LukasGossmann/StepperClock/Documentation/0K20HC30-064B-NK2.5-12.jpg

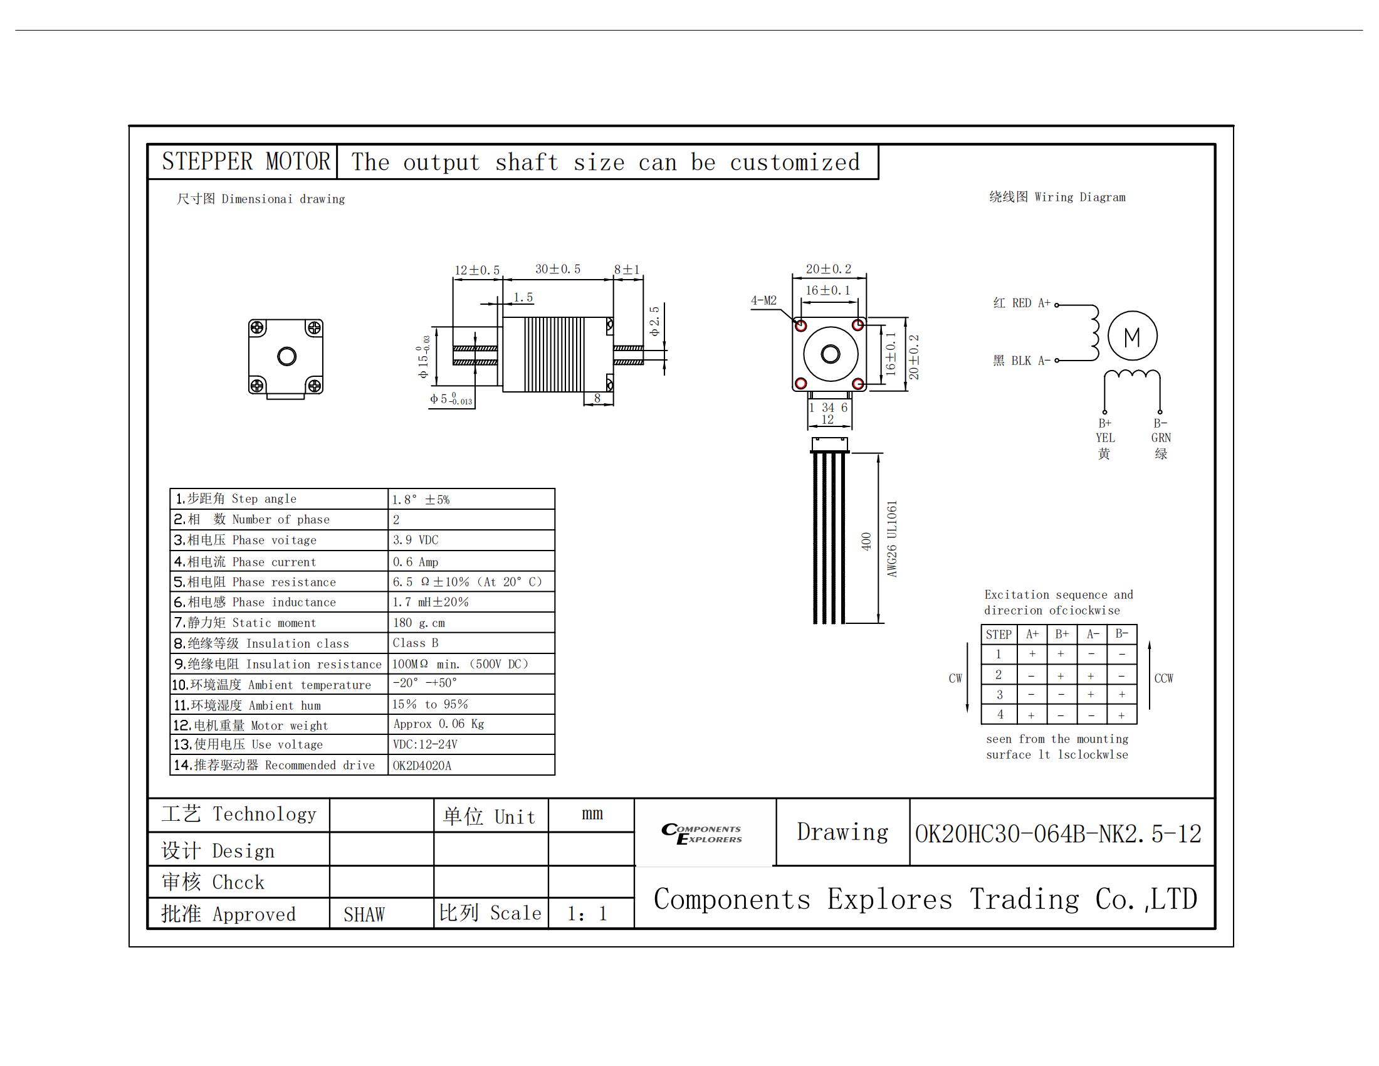
Documentation/0K20HC30-064B-NK2.5-12.jpg
