LukasGossmann/StepperClock/Documentation/0K20STH28-0604B.jpg

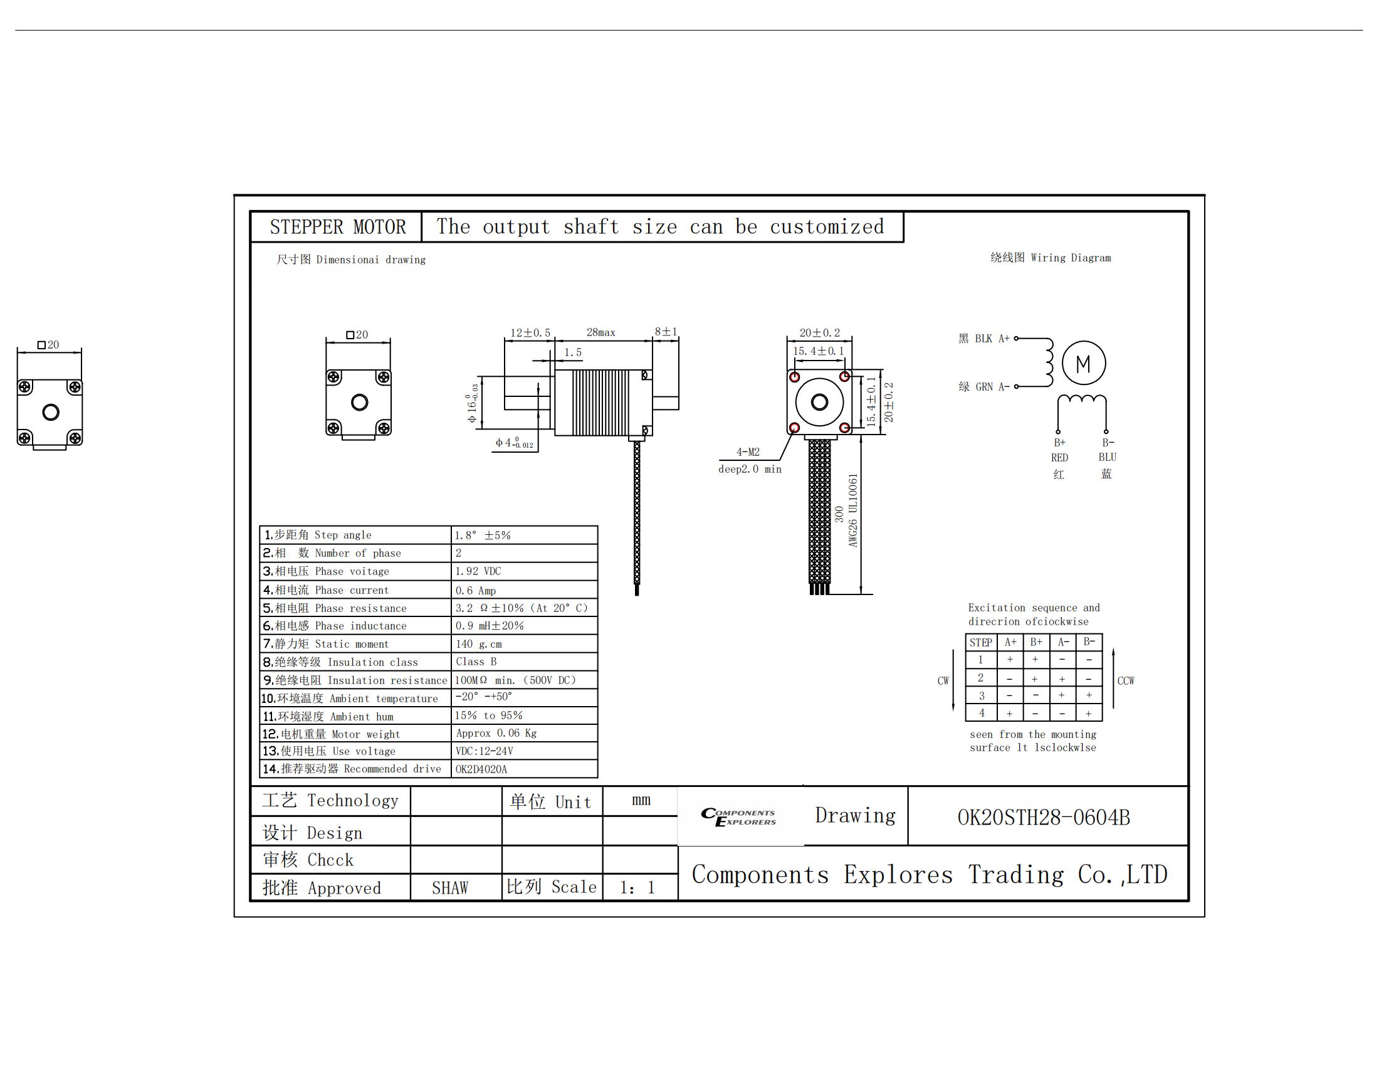
Documentation/0K20STH28-0604B.jpg
