LukasGossmann/StepperClock/Pictures/Backplate rabbet.jpg

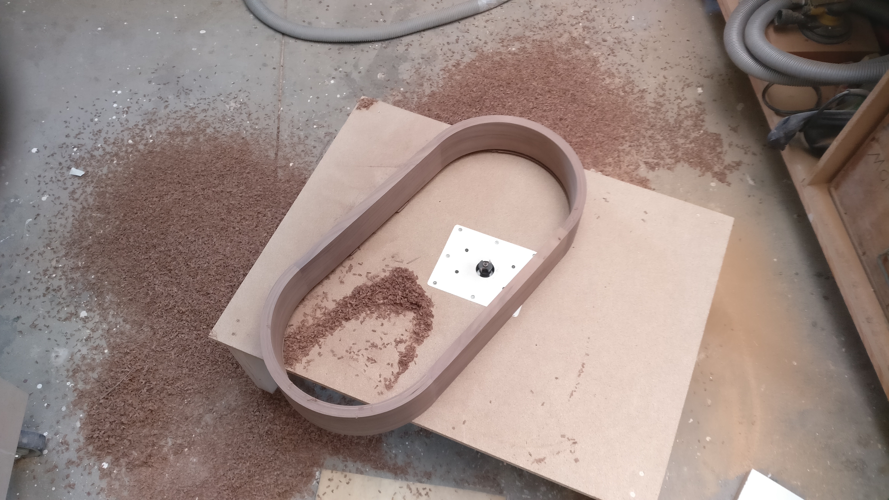
Pictures/Backplate rabbet.jpg
