LukasGossmann/StepperClock/Pictures/Backplate Veneer Back.jpg

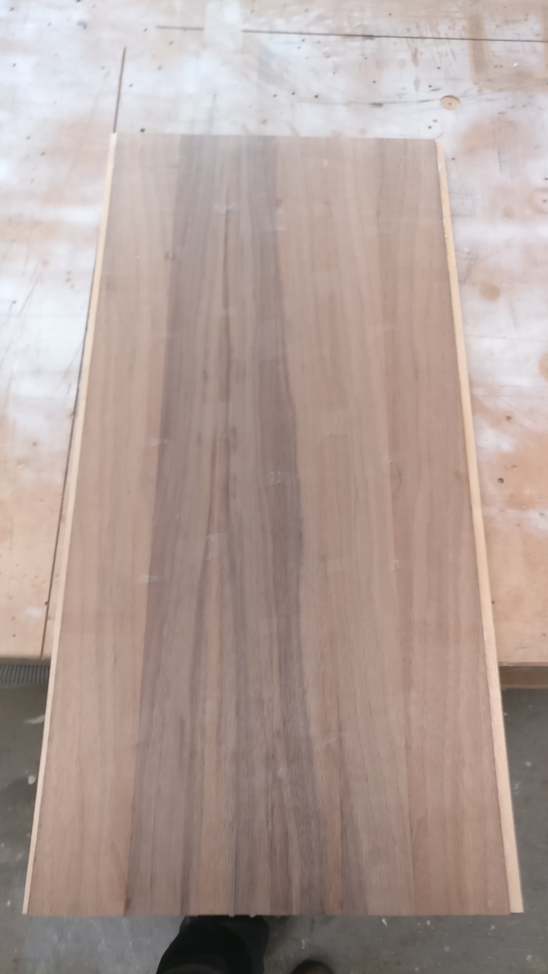
Pictures/Backplate Veneer Back.jpg
