LukasGossmann/StepperClock/Pictures/Bending Fixture 1.jpg

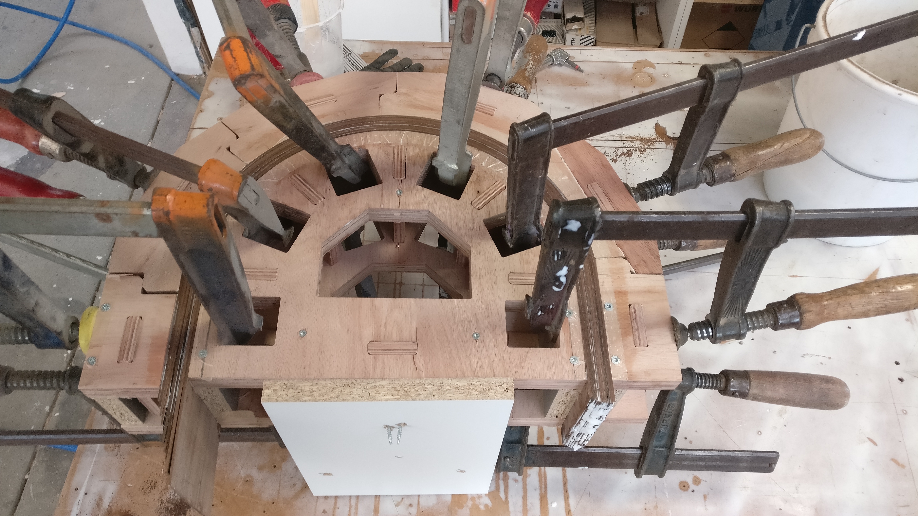
Pictures/Bending Fixture 1.jpg
