LukasGossmann/StepperClock/Pictures/Bending Fixture 2.jpg

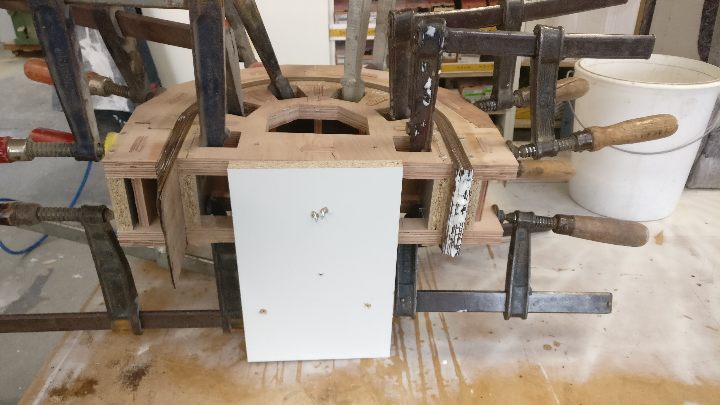
Pictures/Bending Fixture 2.jpg
