LukasGossmann/StepperClock/Pictures/Brass Rind Size.jpg

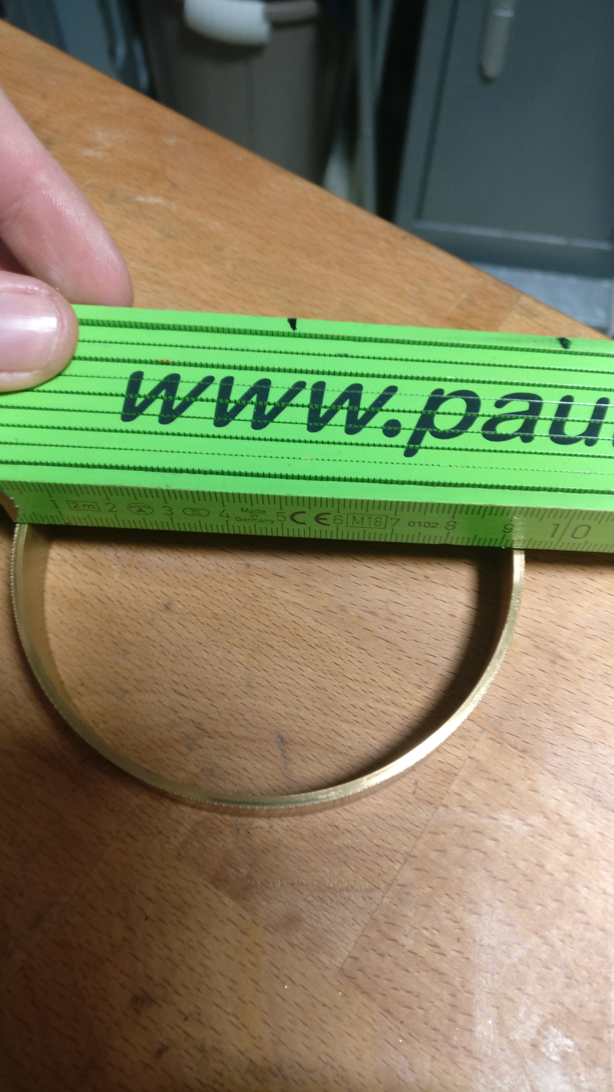
Pictures/Brass Rind Size.jpg
