LukasGossmann/StepperClock/Pictures/Brass Ring.jpg

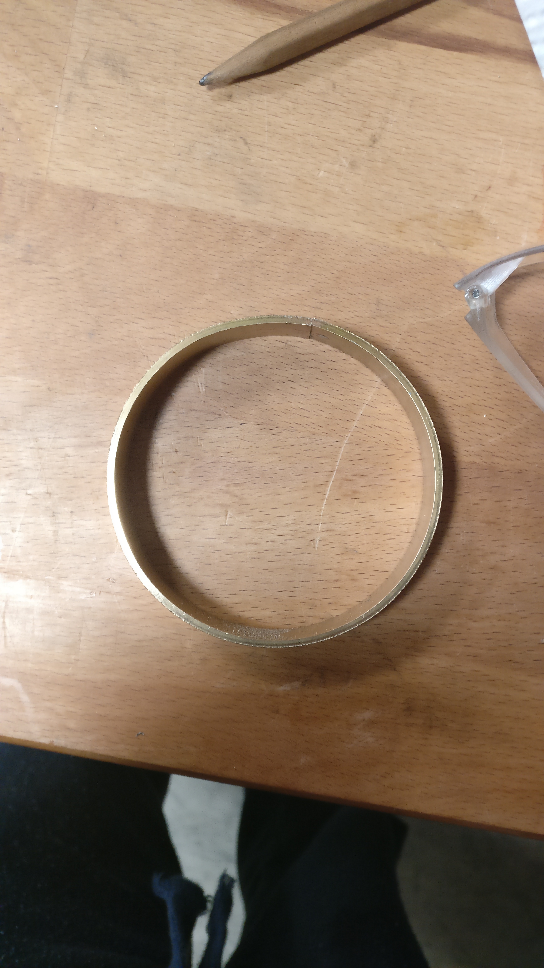
Pictures/Brass Ring.jpg
