LukasGossmann/StepperClock/Pictures/Clock Hands.jpg

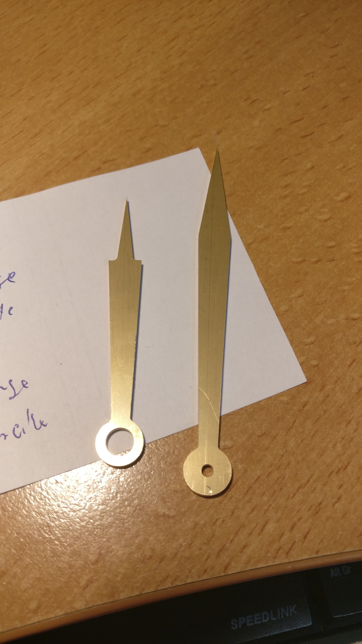
Pictures/Clock Hands.jpg
