LukasGossmann/StepperClock/Pictures/Clock on Wall.jpg

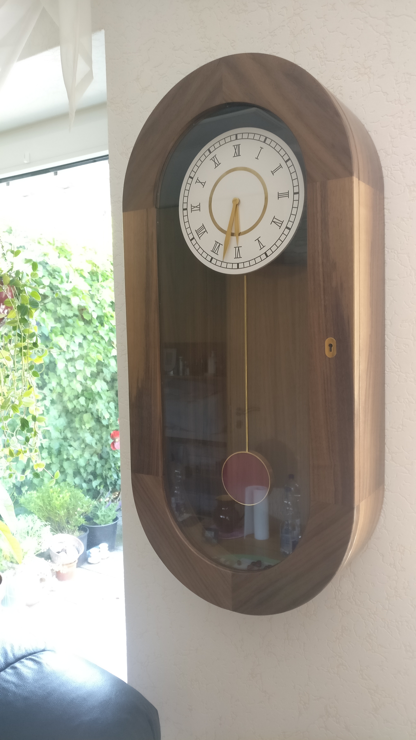
Pictures/Clock on Wall.jpg
