LukasGossmann/StepperClock/Pictures/Clock Render.png

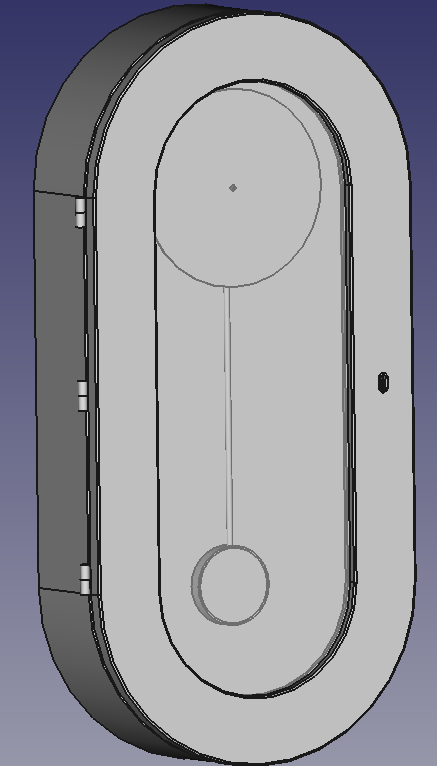
Pictures/Clock Render.png
