LukasGossmann/StepperClock/Pictures/Clockwork/BackView.png

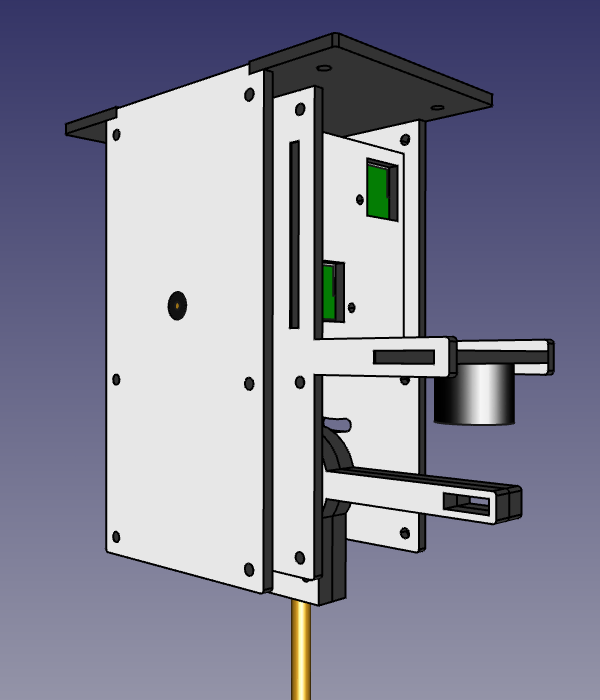
Pictures/Clockwork/BackView.png
