LukasGossmann/StepperClock/Pictures/Clockwork/FrontView.png

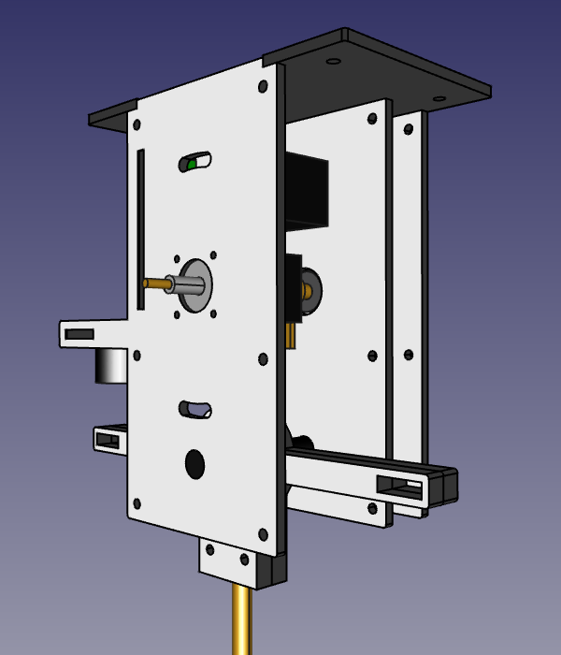
Pictures/Clockwork/FrontView.png
