LukasGossmann/StepperClock/Pictures/Domino Fixture 1.jpg

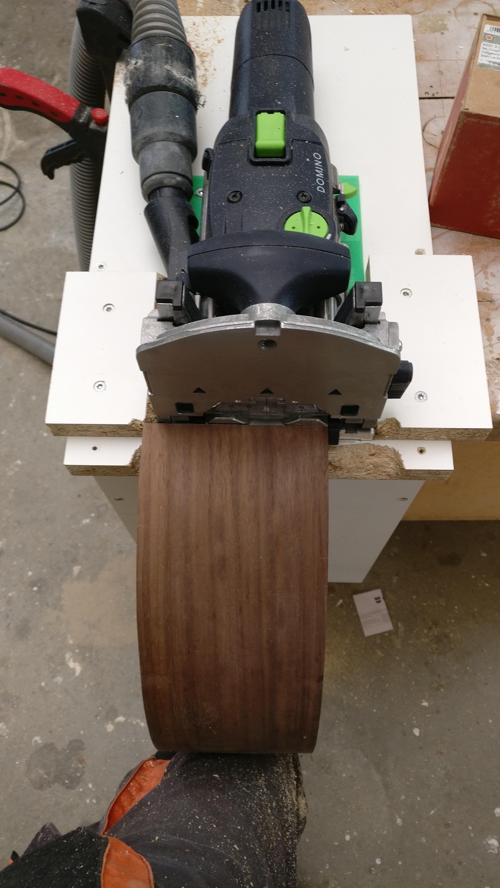
Pictures/Domino Fixture 1.jpg
