LukasGossmann/StepperClock/Pictures/Domino Fixture 2.jpg

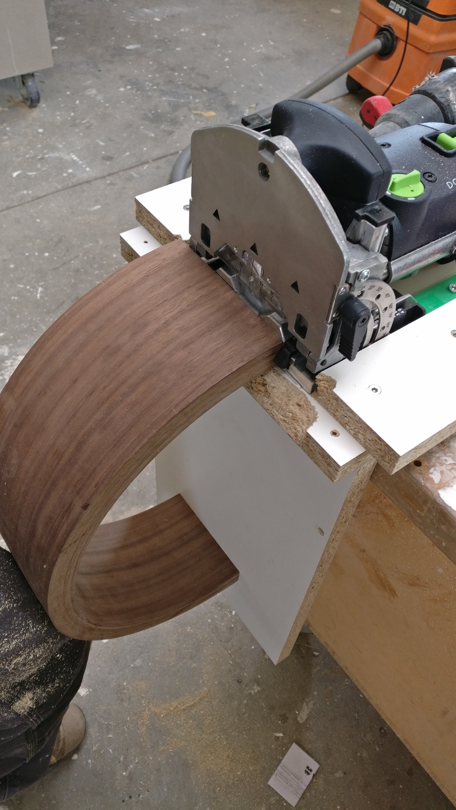
Pictures/Domino Fixture 2.jpg
