LukasGossmann/StepperClock/Pictures/Door glueup.jpg

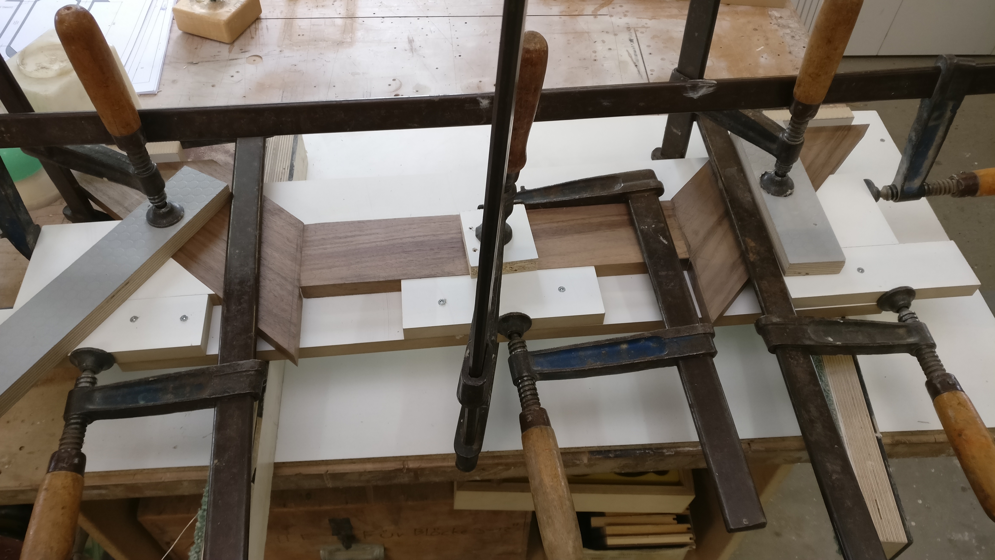
Pictures/Door glueup.jpg
