LukasGossmann/StepperClock/Pictures/Door Hindge.jpg

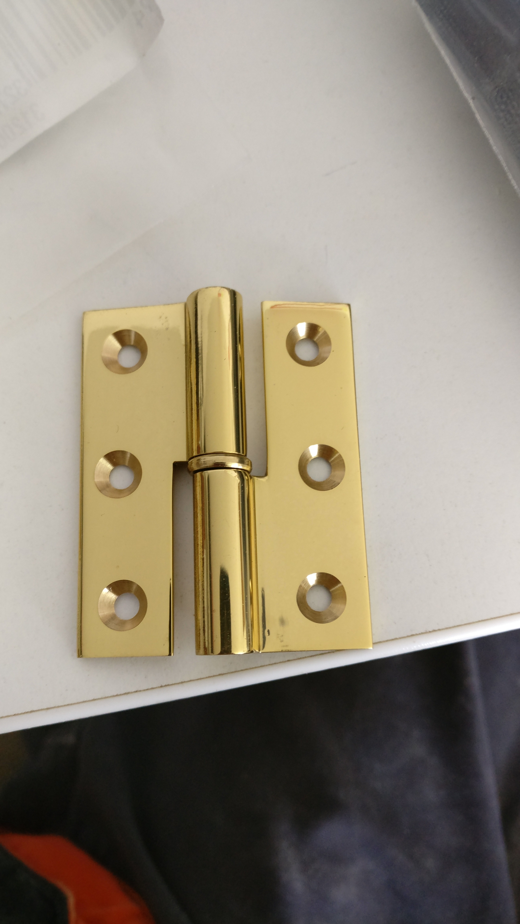
Pictures/Door Hindge.jpg
