LukasGossmann/StepperClock/Pictures/DoorLock/AngledView.png

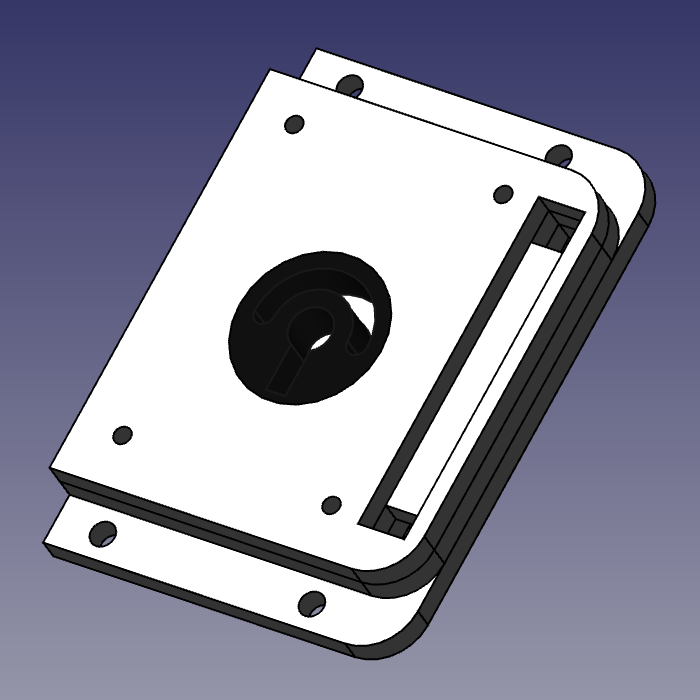
Pictures/DoorLock/AngledView.png
