LukasGossmann/StepperClock/Pictures/DoorLock/AngledView_complete.png

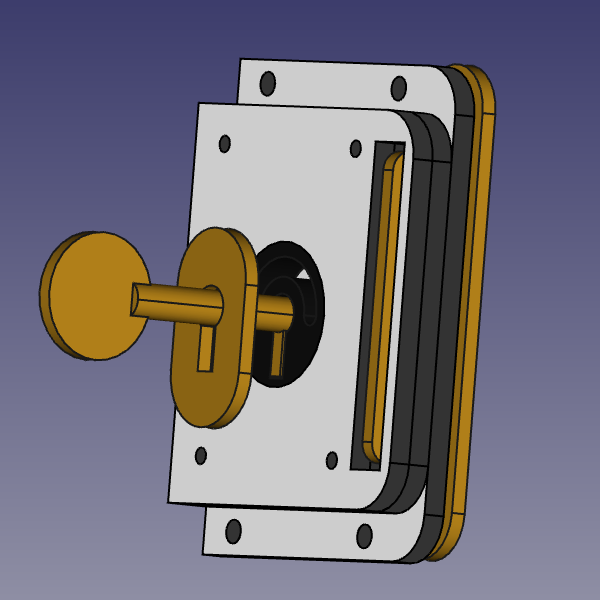
Pictures/DoorLock/AngledView_complete.png
