LukasGossmann/StepperClock/Pictures/Flush trimming bend glueup.jpg

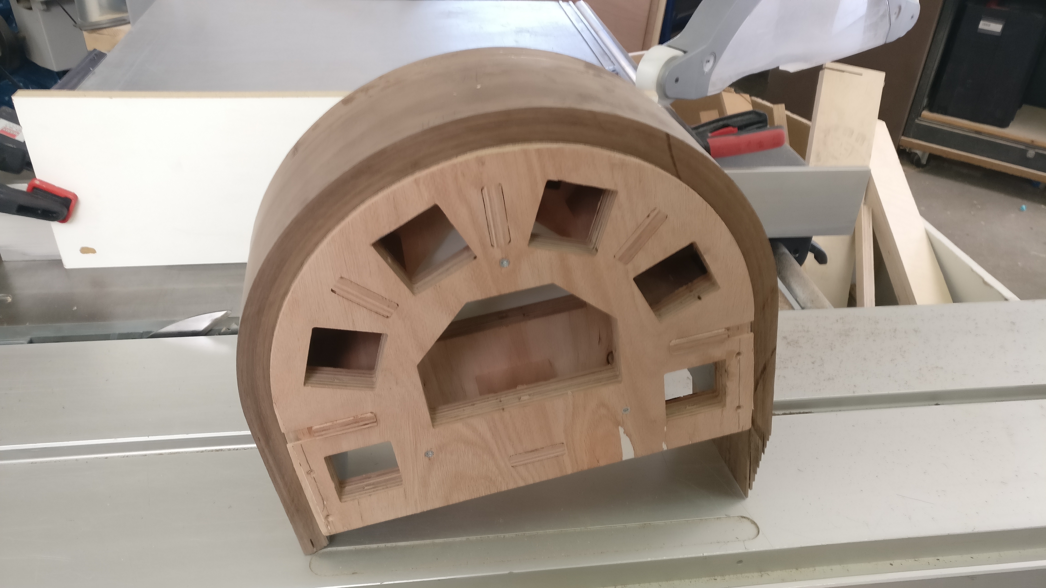
Pictures/Flush trimming bend glueup.jpg
