LukasGossmann/StepperClock/Pictures/Glass Holder Thicknessing Fixure.jpg

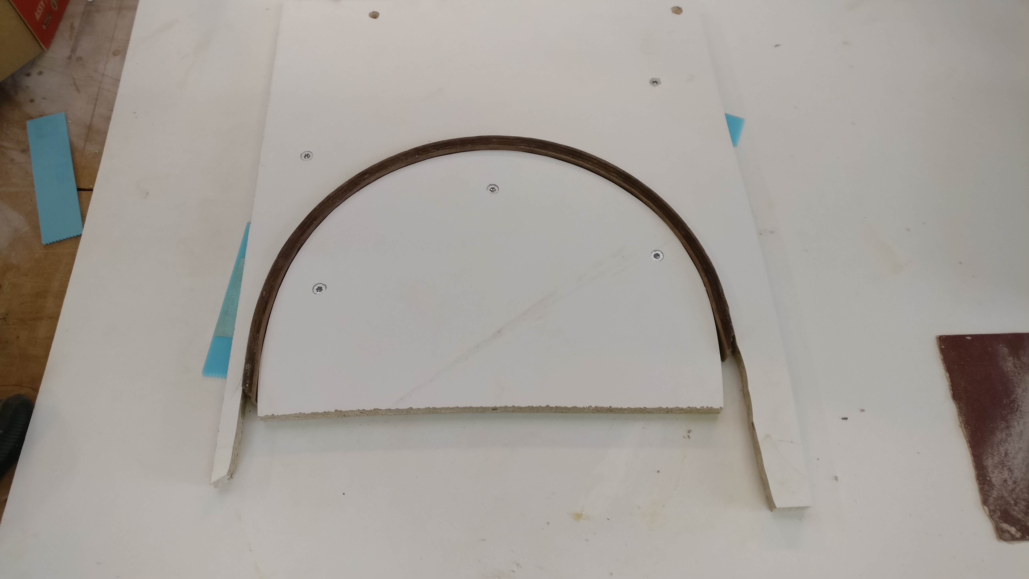
Pictures/Glass Holder Thicknessing Fixure.jpg
