LukasGossmann/StepperClock/Pictures/Key.jpg

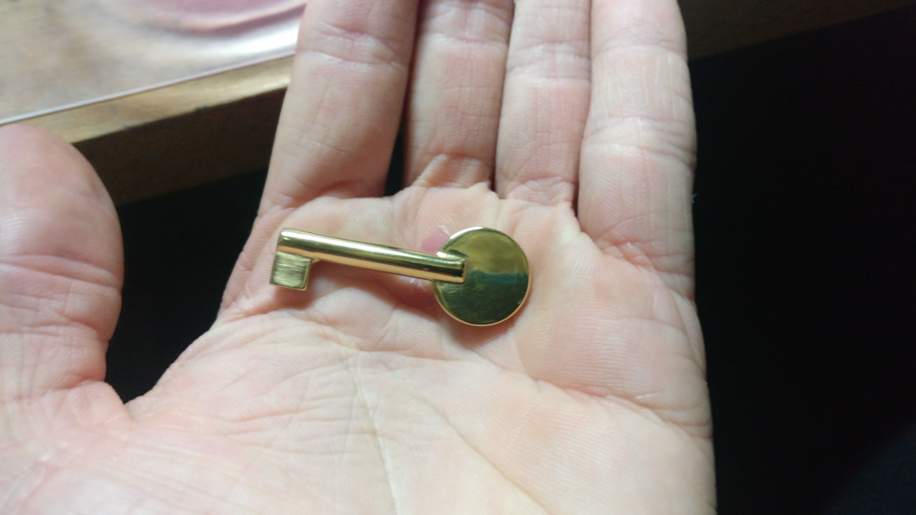
Pictures/Key.jpg
