LukasGossmann/StepperClock/Pictures/Pendulum and Wood Inserts.jpg

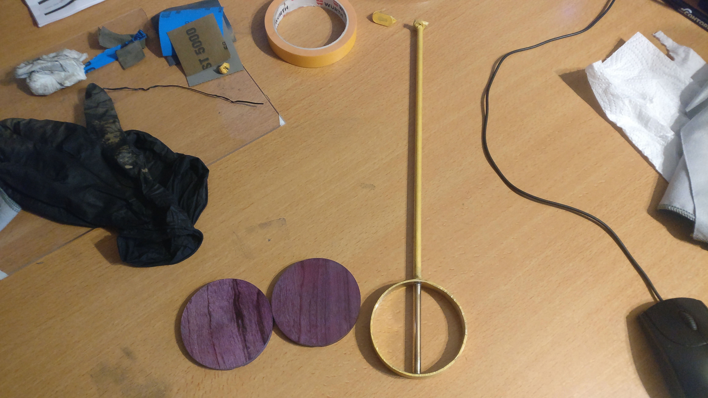
Pictures/Pendulum and Wood Inserts.jpg
