LukasGossmann/StepperClock/Pictures/Clock Testing 2.jpg

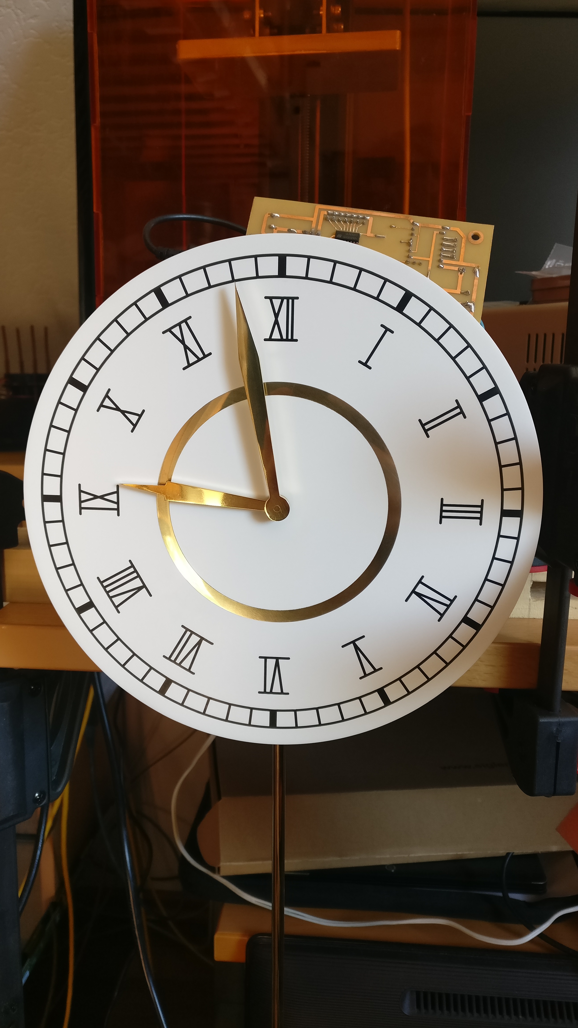
Pictures/Clock Testing 2.jpg
