LukasGossmann/StepperClock/Pictures/Clock Testing.jpg

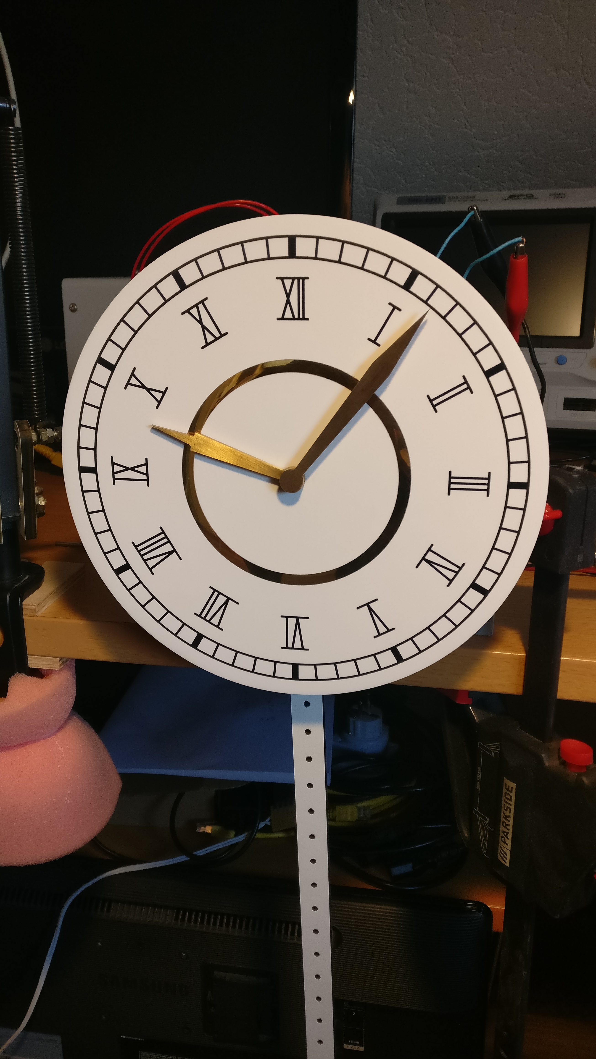
Pictures/Clock Testing.jpg
