LukasGossmann/StepperClock/Pictures/Corian Engraving Test Epoxy.jpg

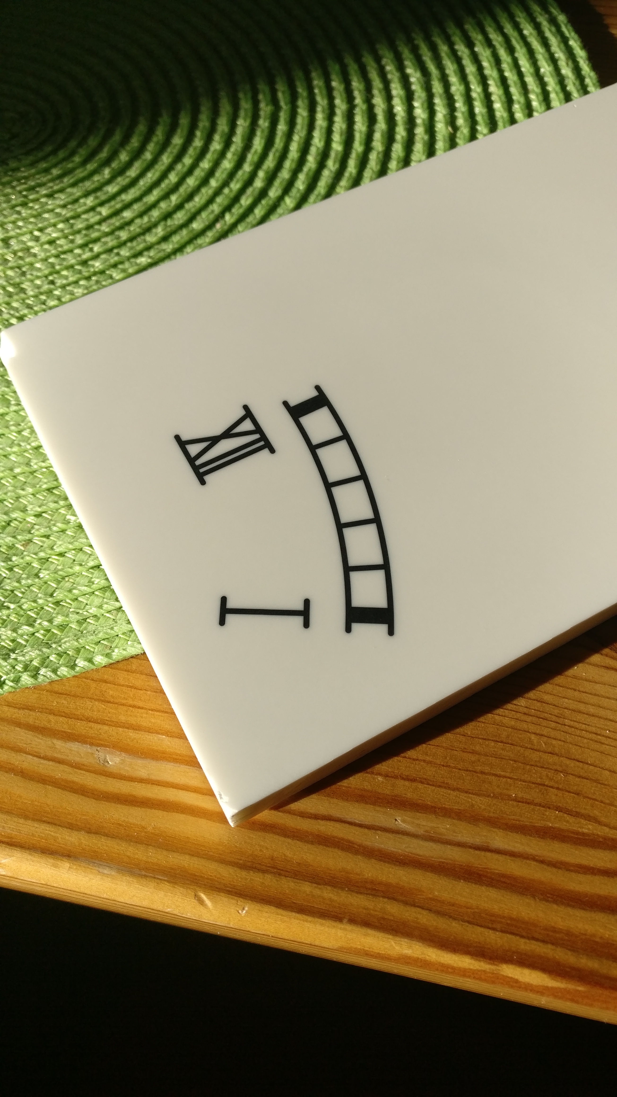
Pictures/Corian Engraving Test Epoxy.jpg
