LukasGossmann/StepperClock/Pictures/Corian Engraving Test.jpg

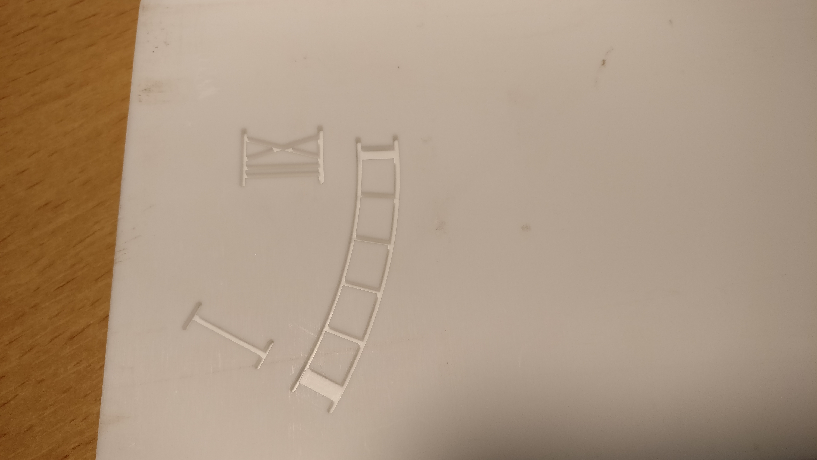
Pictures/Corian Engraving Test.jpg
