LukasGossmann/StepperClock/Pictures/Domino result.jpg

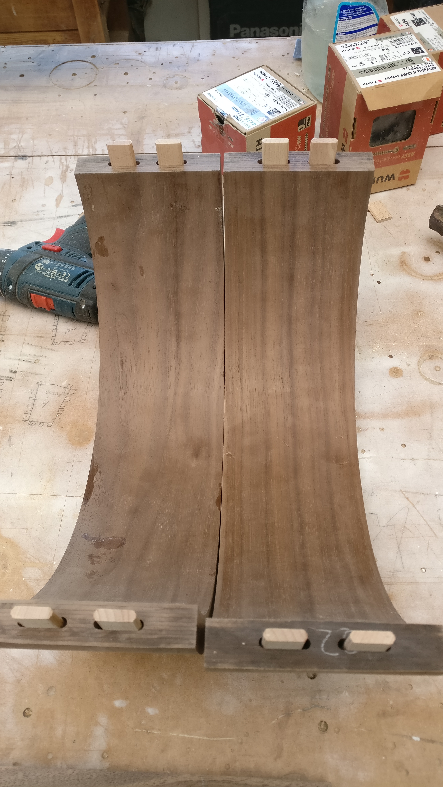
Pictures/Domino result.jpg
