LukasGossmann/StepperClock/Pictures/Flush trimming Door result.jpg

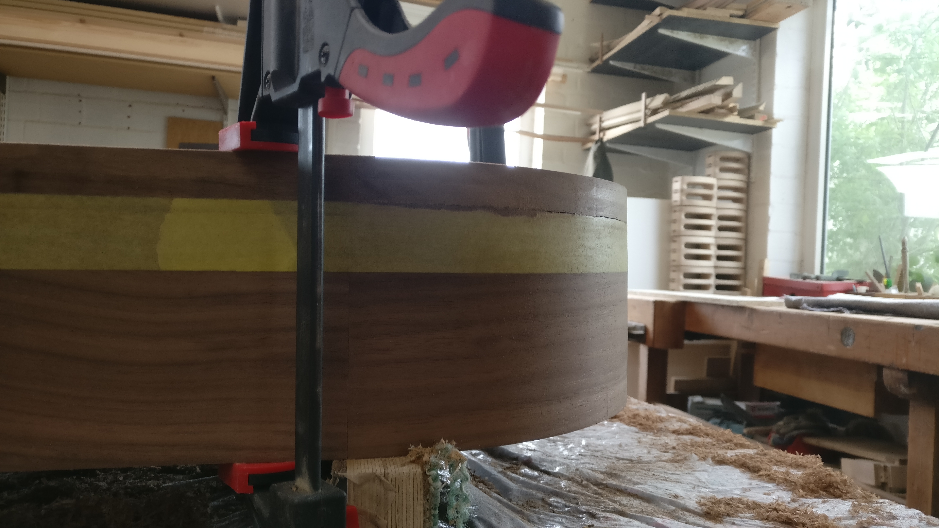
Pictures/Flush trimming Door result.jpg
