LukasGossmann/StepperClock/Pictures/Flush trimming result.jpg

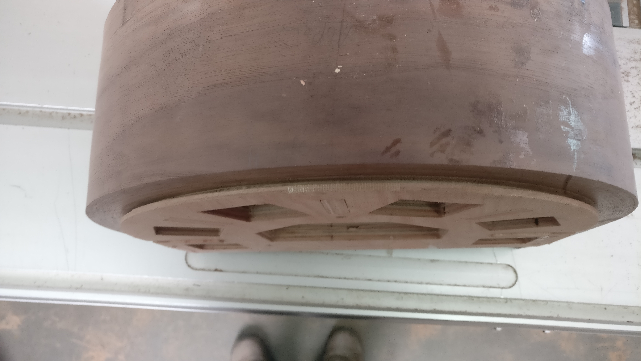
Pictures/Flush trimming result.jpg
